ISPC-Proyect-Integrador-II/Gestion-de-Recursos-Hidricos/C prototipo/Extructura 3D/Archivos editables/[3365] Water Flow Sensor YFS401 Flowmeter Water Flow Transmitter SunRobotics_in.STEP

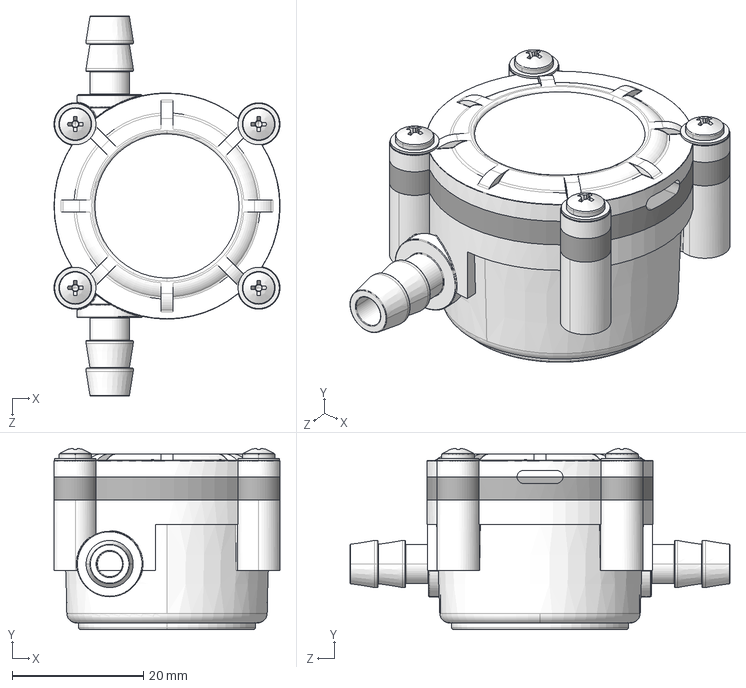
[picture p16: CAD file, 2025-04-24]
C prototipo/Extructura 3D/Archivos editables/[3365] Water Flow Sensor YFS401 Flowmeter Water Flow Transmitter SunRobotics_in.STEP
34.5 x 27.6 x 58.0 mm
