ISPC-Proyect-Integrador-II/Gestion-de-Recursos-Hidricos/C prototipo/Extructura 3D/version 1_1/base_control_box.SLDPRT

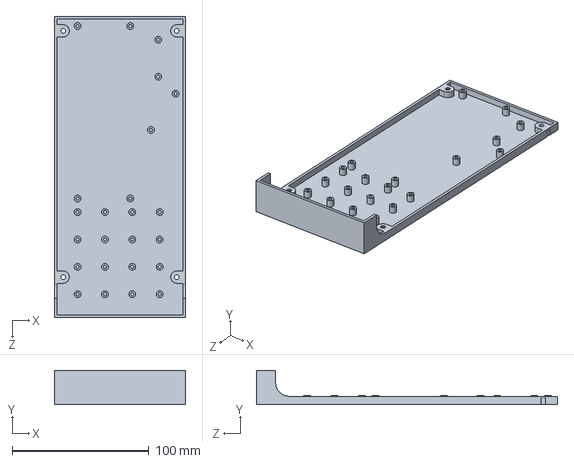
[picture p17: CAD file, 2025-04-24]
C prototipo/Extructura 3D/version 1_1/base_control_box.SLDPRT
96.0 x 25.0 x 220.0 mm
