ISPC-Proyect-Integrador-II/Gestion-de-Recursos-Hidricos/C prototipo/Extructura 3D/version 1_1/Impresiones/STL/cup_holder_fer.STL

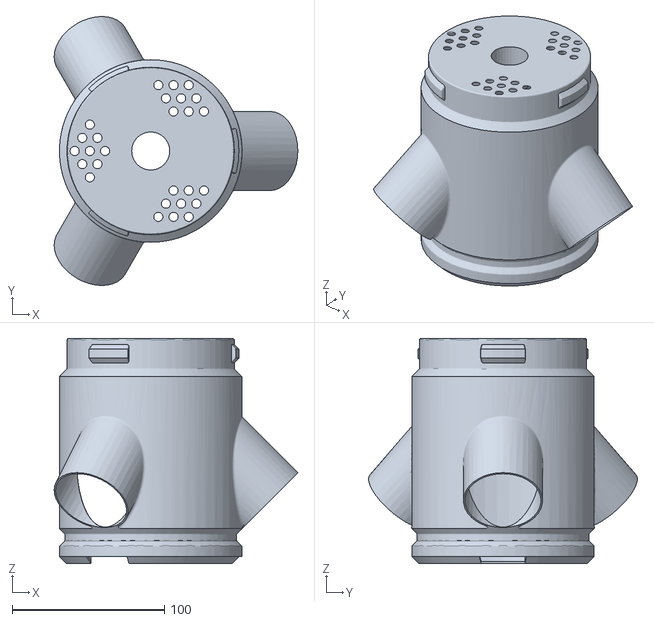
[picture p18: CAD file, 2025-04-24]
C prototipo/Extructura 3D/version 1_1/Impresiones/STL/cup_holder_fer.STL
160.3 x 176.9 x 148.0
