ISPC-Proyect-Integrador-II/Gestion-de-Recursos-Hidricos/C prototipo/Extructura 3D/version 1_1/frente_control_box.SLDPRT

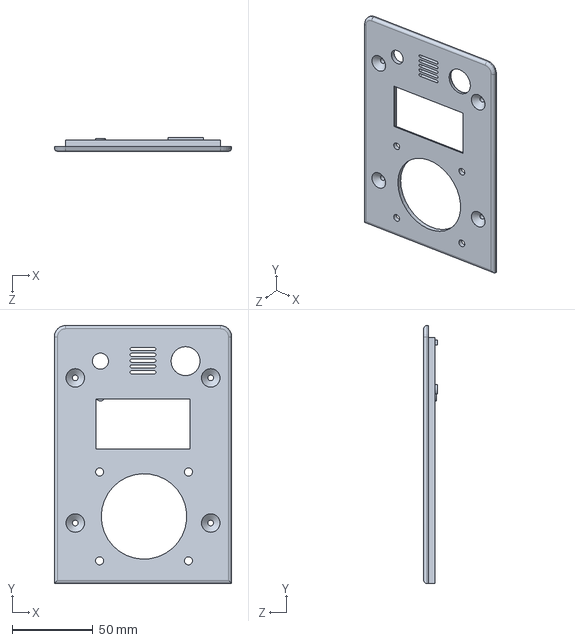
[picture p19: CAD file, 2025-04-24]
C prototipo/Extructura 3D/version 1_1/frente_control_box.SLDPRT
110.0 x 160.0 x 8.50 mm
