ISPC-Proyect-Integrador-II/Gestion-de-Recursos-Hidricos/C prototipo/Extructura 3D/Archivos editables/LoRa_Module_RA-02.SLDPRT

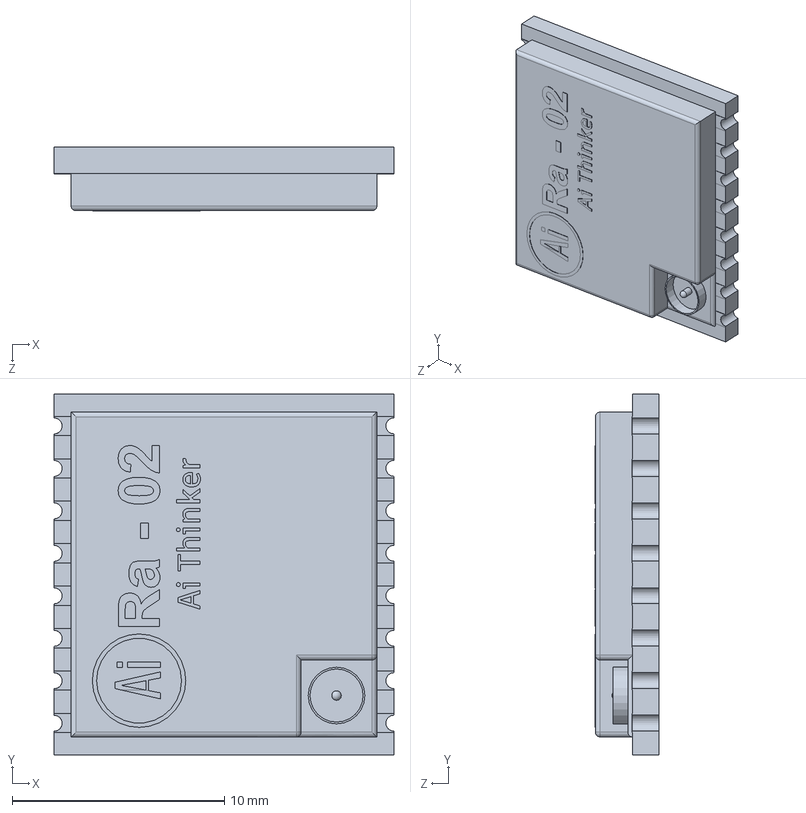
[picture p20: CAD file, 2025-04-24]
C prototipo/Extructura 3D/Archivos editables/LoRa_Module_RA-02.SLDPRT
16.0 x 17.0 x 3.03 mm
