ISPC-Proyect-Integrador-II/Gestion-de-Recursos-Hidricos/C prototipo/Extructura 3D/version 1_1/base.SLDPRT

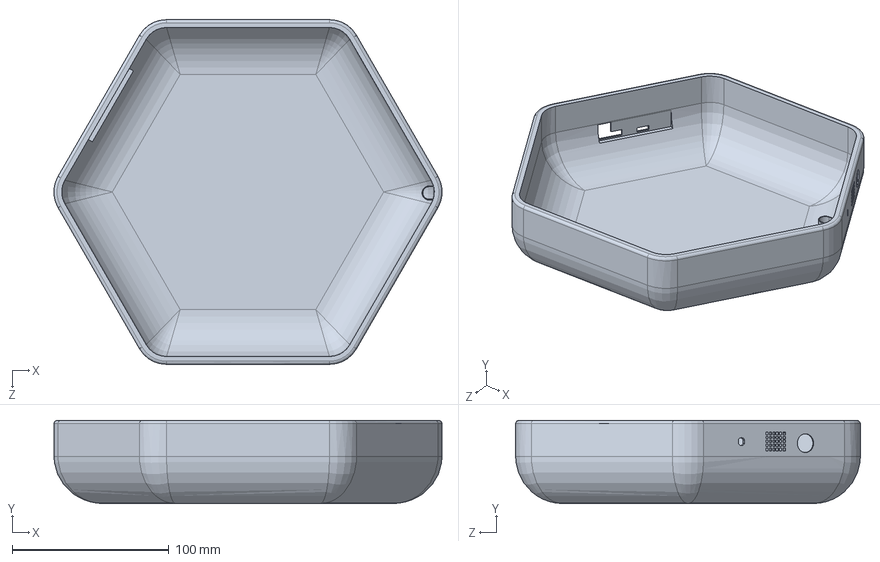
[picture p21: CAD file, 2025-04-19]
C prototipo/Extructura 3D/version 1_1/base.SLDPRT
247.6 x 53.0 x 220.0 mm
