ISPC-Proyect-Integrador-II/Gestion-de-Recursos-Hidricos/C prototipo/Extructura 3D/version 1_1/Impresiones/STL/perilla52.STL

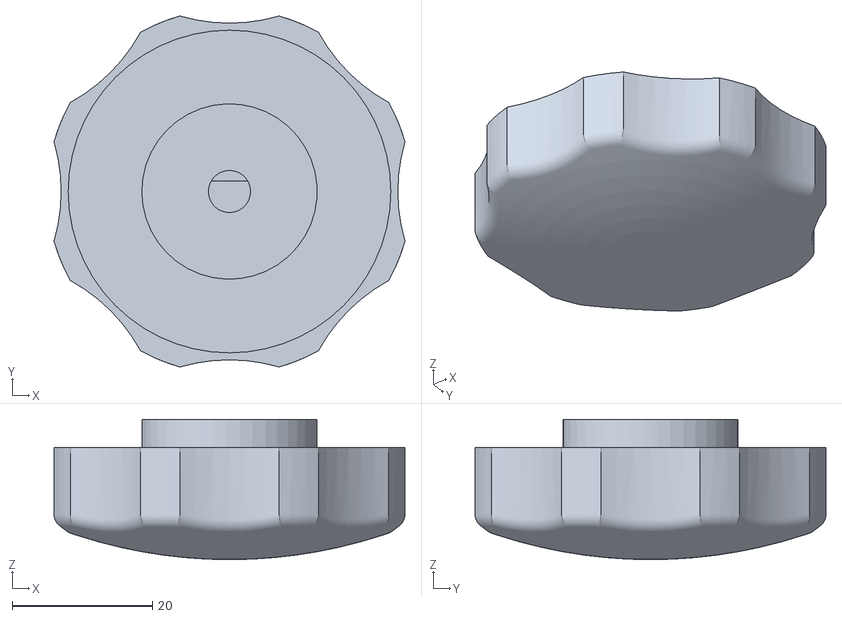
[picture p22: CAD file, 2025-04-24]
C prototipo/Extructura 3D/version 1_1/Impresiones/STL/perilla52.STL
50.0 x 50.0 x 20.0
