ISPC-Proyect-Integrador-II/Gestion-de-Recursos-Hidricos/C prototipo/Extructura 3D/Archivos editables/rodamiento.SLDPRT

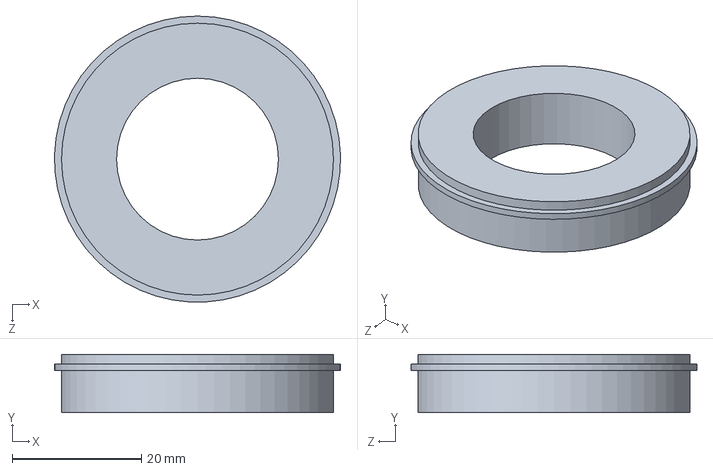
[picture p23: CAD file, 2025-04-23]
C prototipo/Extructura 3D/Archivos editables/rodamiento.SLDPRT
44.2 x 9.00 x 44.2 mm
