ISPC-Proyect-Integrador-II/Gestion-de-Recursos-Hidricos/C prototipo/Extructura 3D/Archivos editables/20-Pin Header - Female - 2.54mm.step

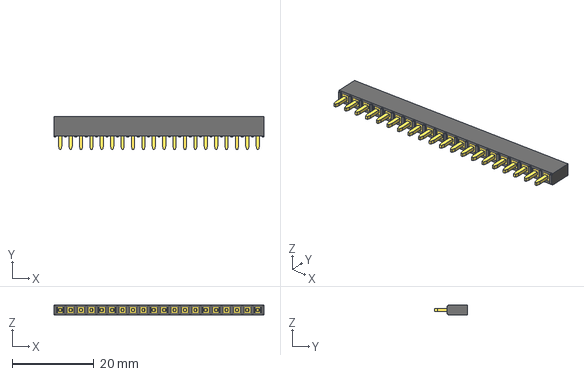
[picture p24: CAD file, 2025-04-21]
C prototipo/Extructura 3D/Archivos editables/20-Pin Header - Female - 2.54mm.step
51.3 x 8.00 x 2.50 mm
