ISPC-Proyect-Integrador-II/Gestion-de-Recursos-Hidricos/C prototipo/Extructura 3D/Archivos editables/placa breadboard.SLDPRT

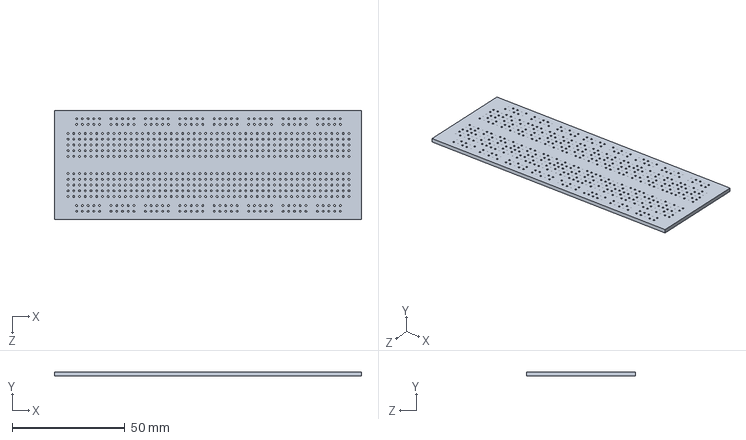
[picture p25: CAD file, 2025-04-21]
C prototipo/Extructura 3D/Archivos editables/placa breadboard.SLDPRT
136.0 x 1.80 x 48.5 mm
