ISPC-Proyect-Integrador-II/Gestion-de-Recursos-Hidricos/C prototipo/Extructura 3D/Archivos editables/LDR.SLDPRT

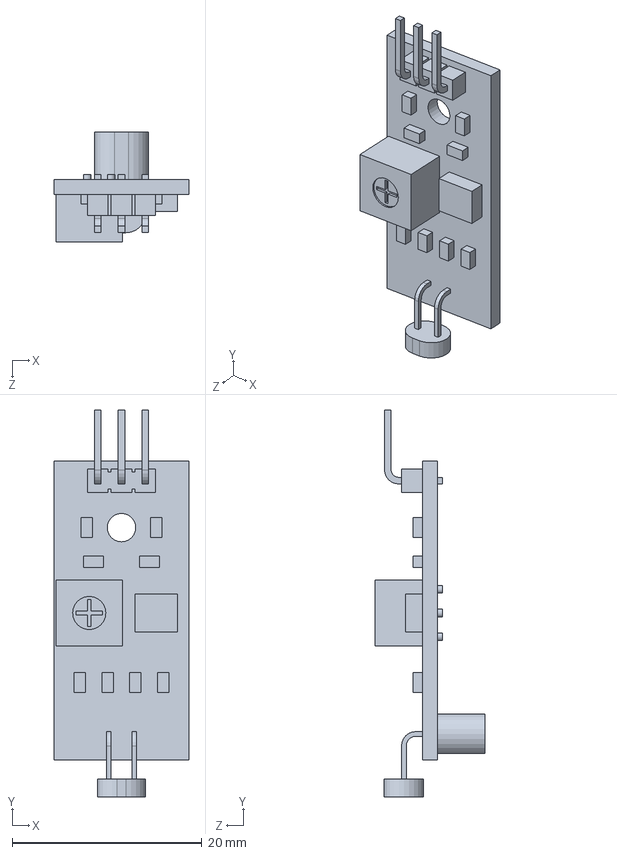
[picture p26: CAD file, 2025-04-21]
C prototipo/Extructura 3D/Archivos editables/LDR.SLDPRT
14.2 x 40.8 x 11.6 mm
