ISPC-Proyect-Integrador-II/Gestion-de-Recursos-Hidricos/C prototipo/Extructura 3D/Archivos editables/SIM800L.SLDPRT

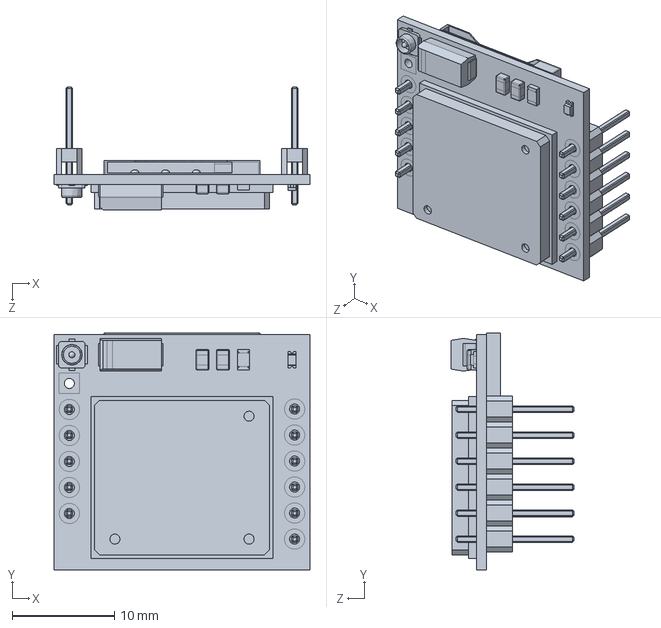
[picture p27: CAD file, 2025-04-21]
C prototipo/Extructura 3D/Archivos editables/SIM800L.SLDPRT
25.0 x 23.1 x 12.0 mm
