ISPC-Proyect-Integrador-II/Gestion-de-Recursos-Hidricos/C prototipo/Extructura 3D/Archivos editables/INA219_I2C_IV_SENSOR_WITH_HEADER.SLDPRT

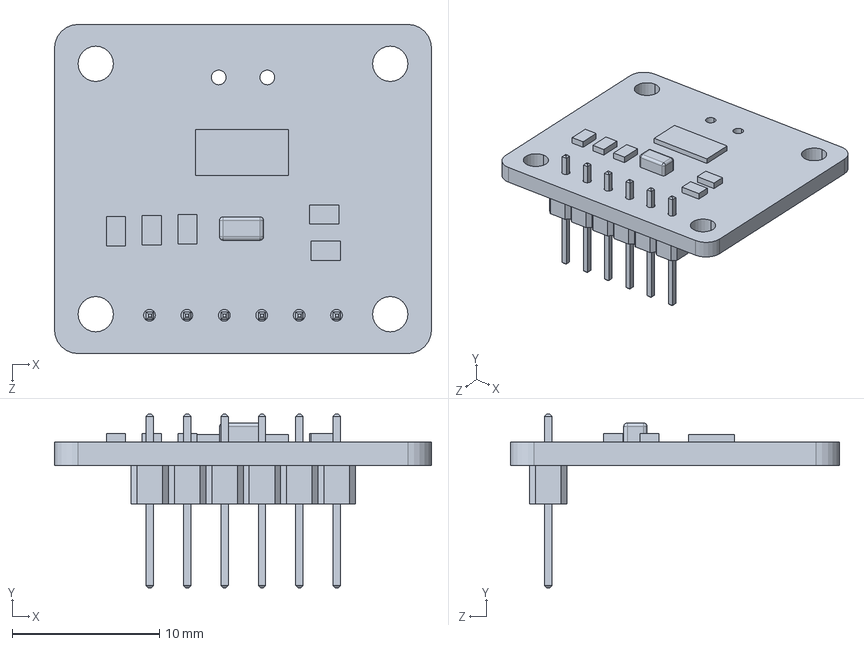
[picture p28: CAD file, 2025-04-21]
C prototipo/Extructura 3D/Archivos editables/INA219_I2C_IV_SENSOR_WITH_HEADER.SLDPRT
25.6 x 11.8 x 22.4 mm
