ISPC-Proyect-Integrador-II/Gestion-de-Recursos-Hidricos/C prototipo/Extructura 3D/Archivos editables/modulo_buzzer_activo.SLDPRT

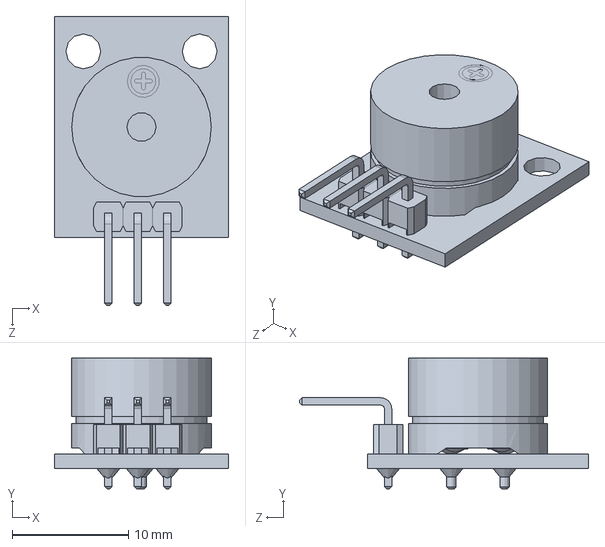
[picture p29: CAD file, 2025-04-21]
C prototipo/Extructura 3D/Archivos editables/modulo_buzzer_activo.SLDPRT
15.0 x 11.2 x 24.8 mm
