ISPC-Proyect-Integrador-II/Gestion-de-Recursos-Hidricos/C prototipo/Extructura 3D/Archivos editables/KY-015.SLDPRT

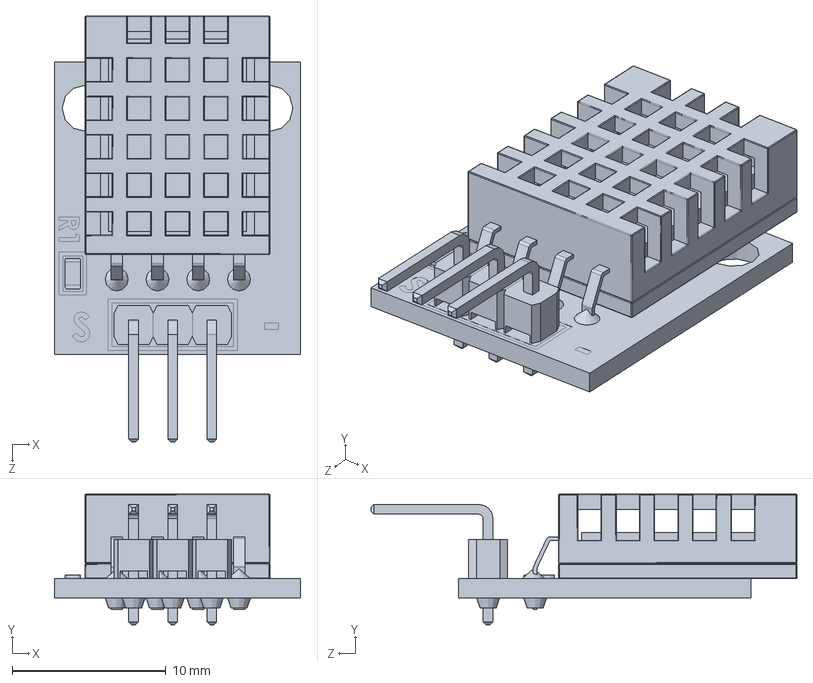
[picture p30: CAD file, 2025-04-19]
C prototipo/Extructura 3D/Archivos editables/KY-015.SLDPRT
16.0 x 8.50 x 27.7 mm
