ISPC-Proyect-Integrador-II/Gestion-de-Recursos-Hidricos/C prototipo/Extructura 3D/Archivos editables/soporte_sensores.SLDPRT

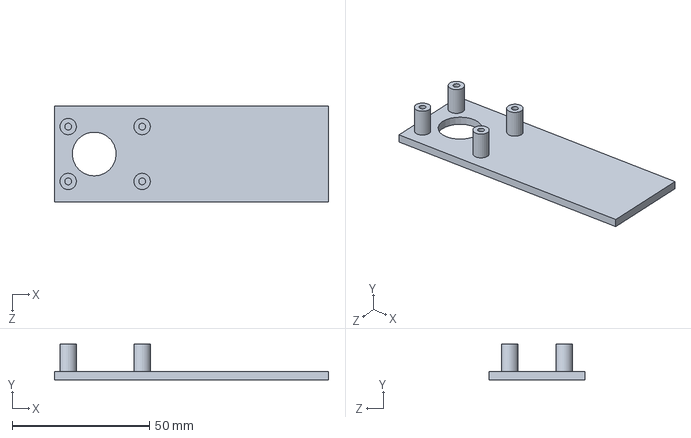
[picture p31: CAD file, 2025-04-19]
C prototipo/Extructura 3D/Archivos editables/soporte_sensores.SLDPRT
100.0 x 13.0 x 35.0 mm
