ISPC-Proyect-Integrador-II/Gestion-de-Recursos-Hidricos/C prototipo/Extructura 3D/Archivos editables/AHT25.SLDPRT

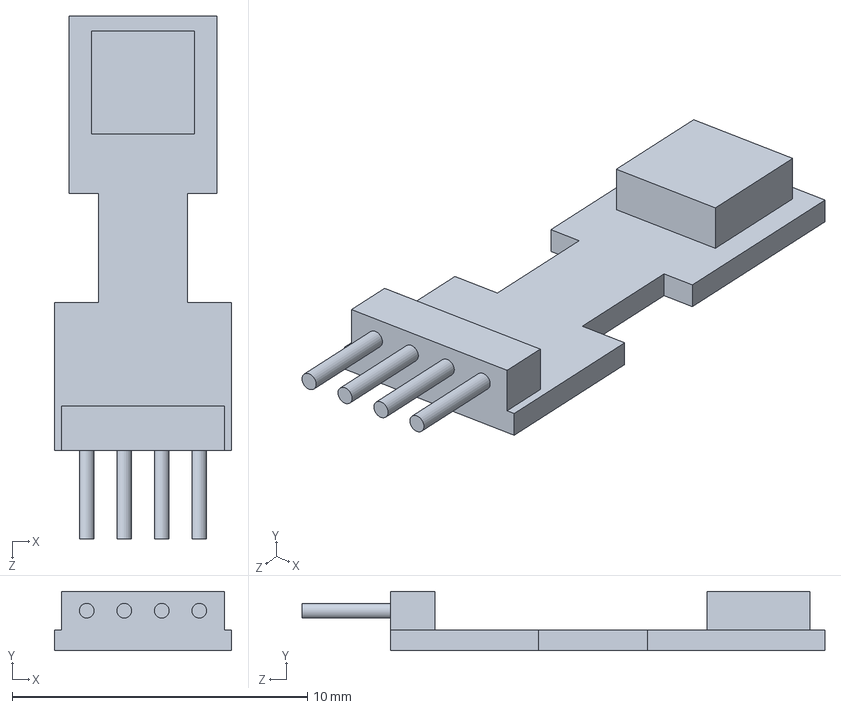
[picture p32: CAD file, 2025-04-19]
C prototipo/Extructura 3D/Archivos editables/AHT25.SLDPRT
6.00 x 2.00 x 17.7 mm
