ISPC-Proyect-Integrador-II/Gestion-de-Recursos-Hidricos/C prototipo/Extructura 3D/Archivos editables/DS18B20.stp

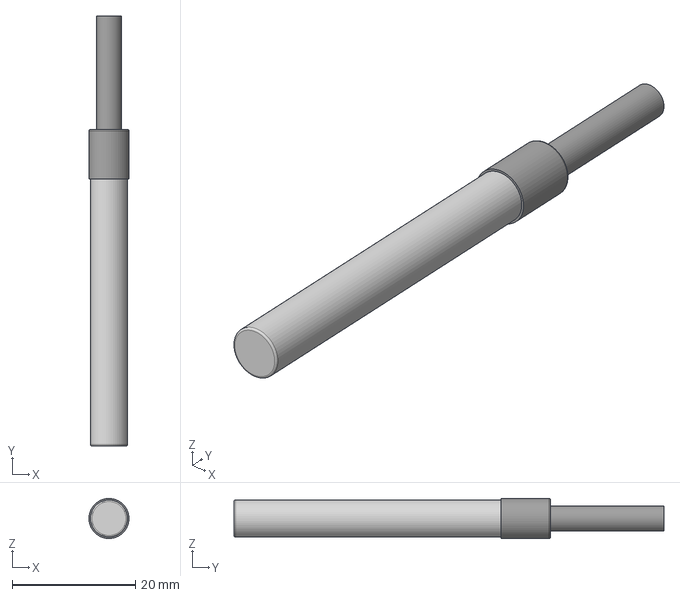
[picture p33: CAD file, 2025-04-18]
C prototipo/Extructura 3D/Archivos editables/DS18B20.stp
6.49 x 69.7 x 6.50 mm
