ISPC-Proyect-Integrador-II/Gestion-de-Recursos-Hidricos/C prototipo/Extructura 3D/Archivos editables/Water level sensor.step

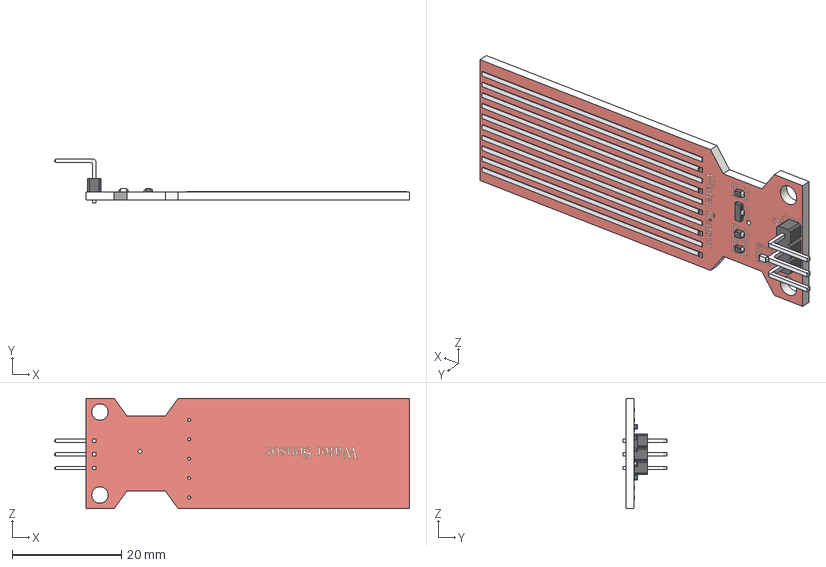
[picture p34: CAD file, 2025-04-18]
C prototipo/Extructura 3D/Archivos editables/Water level sensor.step
65.0 x 8.00 x 20.2 mm
