ISPC-Proyect-Integrador-II/Gestion-de-Recursos-Hidricos/C prototipo/Extructura 3D/Archivos editables/Light sensor LDR v1.step

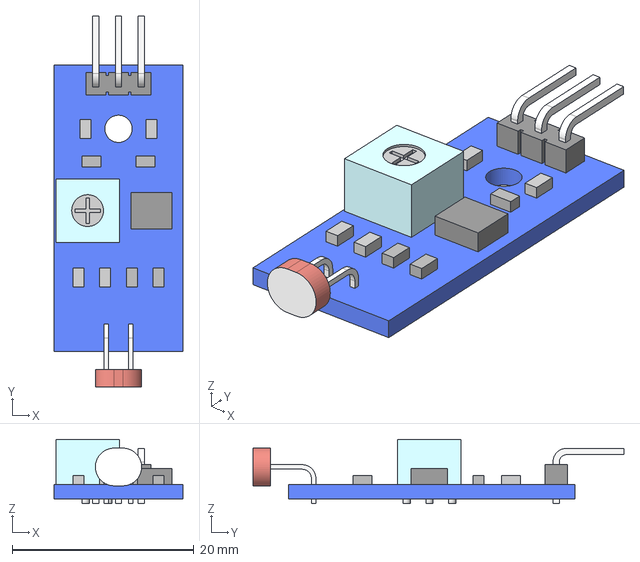
[picture p35: CAD file, 2025-04-18]
C prototipo/Extructura 3D/Archivos editables/Light sensor LDR v1.step
14.2 x 40.8 x 7.10 mm
