ISPC-Proyect-Integrador-II/Gestion-de-Recursos-Hidricos/C prototipo/Extructura 3D/Archivos editables/3_8 inch push connect flow meter.step

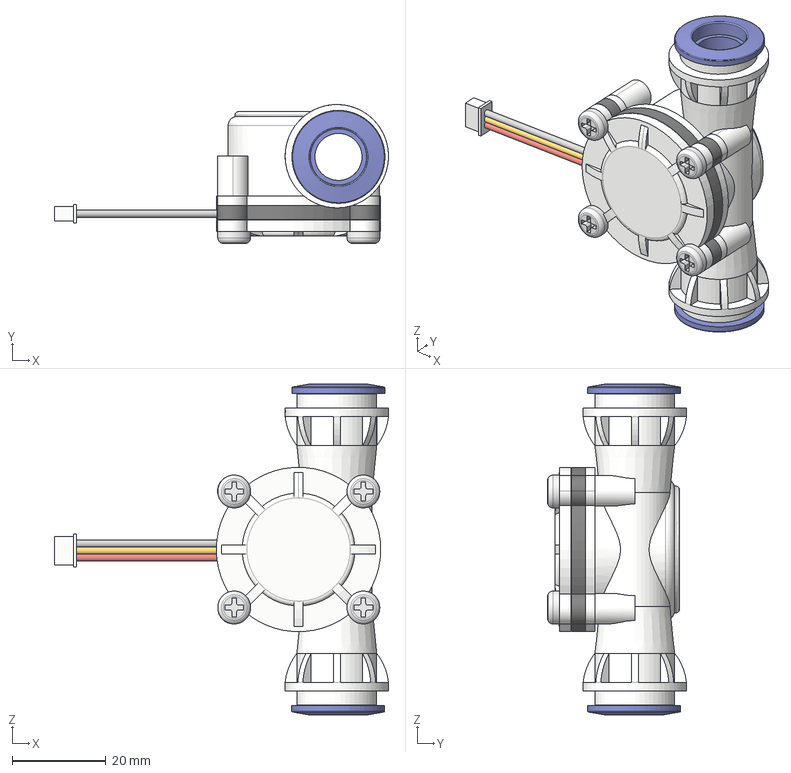
[picture p36: CAD file, 2025-04-18]
C prototipo/Extructura 3D/Archivos editables/3_8 inch push connect flow meter.step
71.1 x 29.6 x 70.4 mm
