ISPC-Proyect-Integrador-II/Gestion-de-Recursos-Hidricos/C prototipo/Extructura 3D/Archivos editables/MQ135_sensor.step

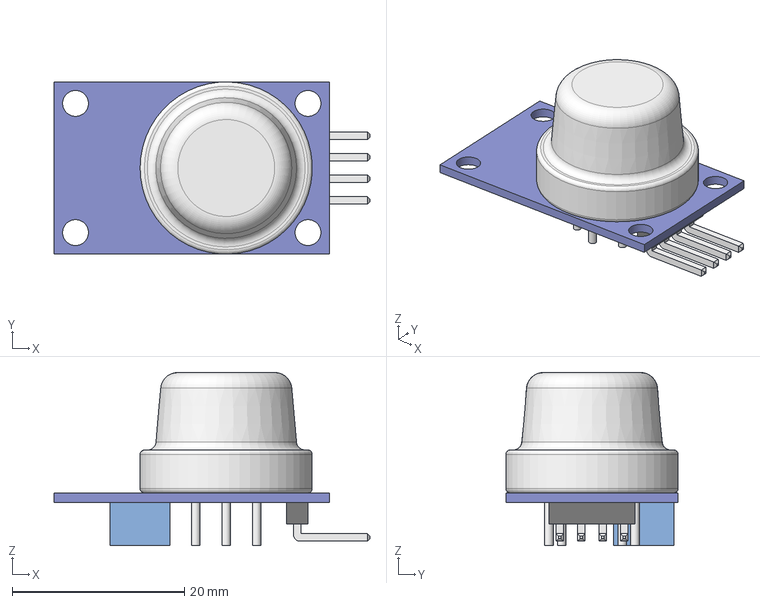
[picture p37: CAD file, 2025-04-18]
C prototipo/Extructura 3D/Archivos editables/MQ135_sensor.step
36.7 x 20.0 x 20.1 mm
