ISPC-Proyect-Integrador-II/Gestion-de-Recursos-Hidricos/C prototipo/Extructura 3D/Archivos editables/Rotary Encoder - KY-040.step

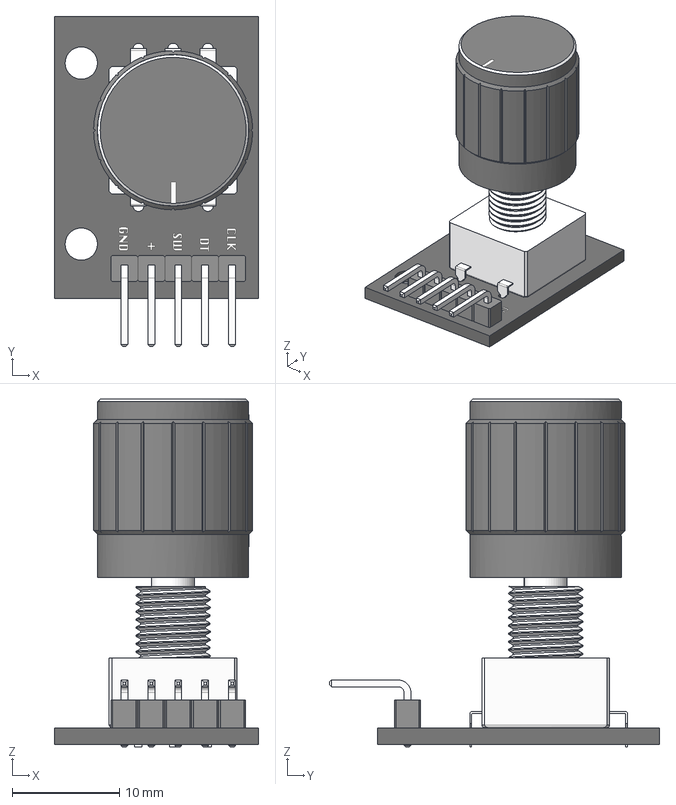
[picture p38: CAD file, 2025-04-18]
C prototipo/Extructura 3D/Archivos editables/Rotary Encoder - KY-040.step
19.0 x 30.8 x 32.4 mm
