ISPC-Proyect-Integrador-II/Gestion-de-Recursos-Hidricos/C prototipo/Extructura 3D/Archivos editables/Soil Humidty sensor.SLDPRT

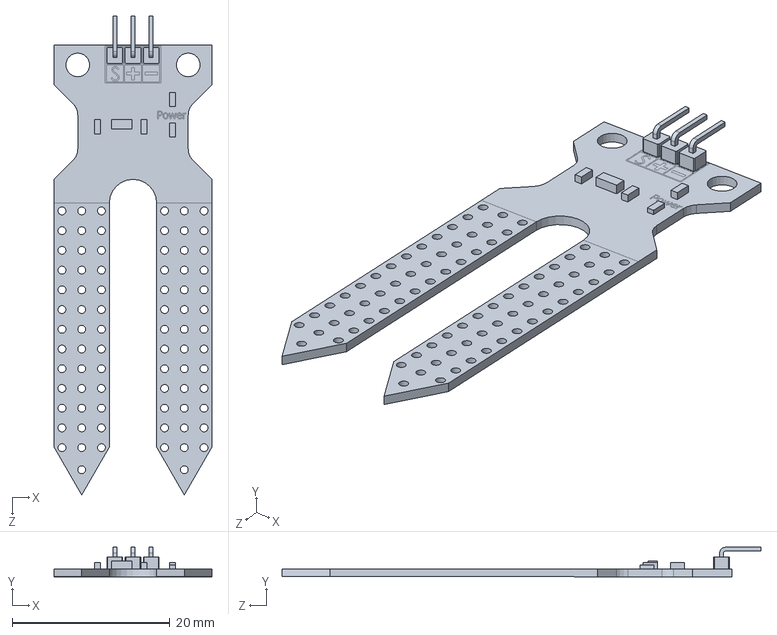
[picture p39: CAD file, 2025-04-17]
C prototipo/Extructura 3D/Archivos editables/Soil Humidty sensor.SLDPRT
20.0 x 3.75 x 60.7 mm
