ISPC-Proyect-Integrador-II/Gestion-de-Recursos-Hidricos/C prototipo/prueba/Hidroponia/include/Configuración_avanzada.h

#ifndef CONFIGURACION_AVANZADA_H
#define CONFIGURACION_AVANZADA_H

// Configuración avanzada y parámetros de calibración

// Calibración del sensor de pH
#define PH_CALIBRATION 7.0

// Otros parámetros avanzados de calibración para sensores o ajustes finos
#define TEMP_CALIBRATION 25.0

#endif 
